Floyd-Fish/EVMeter/Software/EVMeter_V2.1/Drivers/tcs34725/tcs34725.h

#ifndef __TCS34725__H
#define __TCS34725__H

#include "main.h"

extern I2C_HandleTypeDef hi2c1;
#define TCS34725_I2C_PORT &hi2c1

#define TCS34725_ADDR (0x29<<1)     /**< I2C address **/
#define TCS34725_COMMAND_BIT (0x80) /**< Command bit **/

#define TCS34725_ENABLE (0x00)      /**< Interrupt Enable register */
#define TCS34725_ENABLE_AIEN (0x10) /**< RGBC Interrupt Enable */
#define TCS34725_ENABLE_WEN                                                    \
  (0x08) /**< Wait Enable - Writing 1 activates the wait timer */
#define TCS34725_ENABLE_AEN                                                    \
  (0x02) /**< RGBC Enable - Writing 1 actives the ADC, 0 disables it */
#define TCS34725_ENABLE_PON                                                    \
  (0x01) /**< Power on - Writing 1 activates the internal oscillator, 0        \
            disables it */
#define TCS34725_ATIME (0x01) /**< Integration time */
#define TCS34725_WTIME                                                         \
  (0x03) /**< Wait time (if TCS34725_ENABLE_WEN is asserted) */
#define TCS34725_WTIME_2_4MS (0xFF) /**< WLONG0 = 2.4ms   WLONG1 = 0.029s */
#define TCS34725_WTIME_204MS (0xAB) /**< WLONG0 = 204ms   WLONG1 = 2.45s  */
#define TCS34725_WTIME_614MS (0x00) /**< WLONG0 = 614ms   WLONG1 = 7.4s   */
#define TCS34725_AILTL                                                         \
  (0x04) /**< Clear channel lower interrupt threshold (lower byte) */
#define TCS34725_AILTH                                                         \
  (0x05) /**< Clear channel lower interrupt threshold (higher byte) */
#define TCS34725_AIHTL                                                         \
  (0x06) /**< Clear channel upper interrupt threshold (lower byte) */
#define TCS34725_AIHTH                                                         \
  (0x07) /**< Clear channel upper interrupt threshold (higher byte) */

#define TCS34725_CONFIG (0x0D) /**< Configuration **/
#define TCS34725_CONFIG_WLONG                                                  \
  (0x02) /**< Choose between short and long (12x) wait times via               \
            TCS34725_WTIME */
#define TCS34725_CONTROL (0x0F) /**< Set the gain level for the sensor */
#define TCS34725_ID                                                            \
  (0x12) /**< 0x44 = TCS34721/TCS34725, 0x4D = TCS34723/TCS34727 */
#define TCS34725_STATUS (0x13)      /**< Device status **/
#define TCS34725_STATUS_AINT (0x10) /**< RGBC Clean channel interrupt */
#define TCS34725_STATUS_AVALID                                                 \
  (0x01) /**< Indicates that the RGBC channels have completed an integration   \
            cycle */
#define TCS34725_CDATAL (0x14) /**< Clear channel data low byte */
#define TCS34725_CDATAH (0x15) /**< Clear channel data high byte */
#define TCS34725_RDATAL (0x16) /**< Red channel data low byte */
#define TCS34725_RDATAH (0x17) /**< Red channel data high byte */
#define TCS34725_GDATAL (0x18) /**< Green channel data low byte */
#define TCS34725_GDATAH (0x19) /**< Green channel data high byte */
#define TCS34725_BDATAL (0x1A) /**< Blue channel data low byte */
#define TCS34725_BDATAH (0x1B) /**< Blue channel data high byte */

/** Integration time settings for TCS34725 */
typedef enum {
    TCS34725_INTEGRATIONTIME_2_4MS =
    0xFF, /**<  2.4ms - 1 cycle    - Max Count: 1024  */
    TCS34725_INTEGRATIONTIME_24MS =
    0xF6, /**<  24ms  - 10 cycles  - Max Count: 10240 */
    TCS34725_INTEGRATIONTIME_50MS =
    0xEB, /**<  50ms  - 20 cycles  - Max Count: 20480 */
    TCS34725_INTEGRATIONTIME_101MS =
    0xD5, /**<  101ms - 42 cycles  - Max Count: 43008 */
    TCS34725_INTEGRATIONTIME_154MS =
    0xC0, /**<  154ms - 64 cycles  - Max Count: 65535 */
    TCS34725_INTEGRATIONTIME_700MS =
    0x00 /**<  700ms - 256 cycles - Max Count: 65535 */
} tcs34725IntegrationTime_t;

/** Gain settings for TCS34725  */
typedef enum {
    TCS34725_GAIN_1X = 0x00,  /**<  No gain  */
    TCS34725_GAIN_4X = 0x01,  /**<  4x gain  */
    TCS34725_GAIN_16X = 0x02, /**<  16x gain */
    TCS34725_GAIN_60X = 0x03  /**<  60x gain */
} tcs34725Gain_t;

void TCS34725_Init(void);
void TCS34725_Enable(void);
void TCS34725_Disable(void);
void TCS34725_SetIntegrationTime(uint8_t itime);
void TCS34725_SetGain(uint8_t gain);
void TCS34725_GetRawData(uint16_t *r, uint16_t *g, uint16_t *b,
                         uint16_t *c);
void TCS34725_GetRGB(float *r, float *g, float *b);
uint16_t TCS34725_CalcColorTemp(uint16_t r, uint16_t g, uint16_t b);
uint16_t TCS34725_CalcColorTemp_DN40(uint16_t r, uint16_t g,
                                     uint16_t b, uint16_t c);
float TCS34725_CalcLux(uint16_t r, uint16_t g, uint16_t b);

#endif
